alinxalinx/AXU2CGA_AXU2CGB/linux/.images_for_documents/60.png

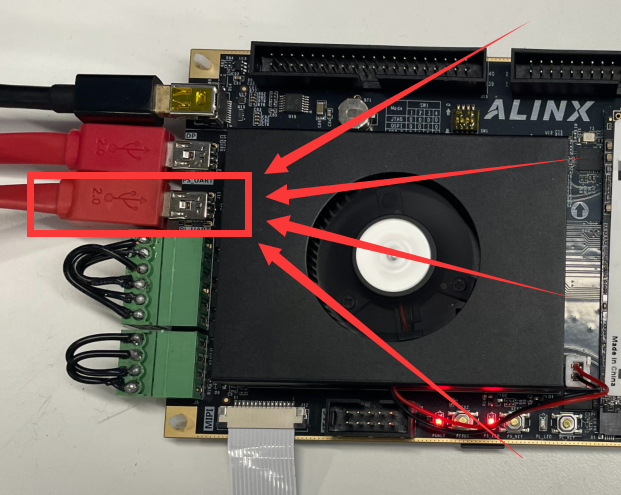
linux/.images_for_documents/60.png
