alinxalinx/AXU2CGA_AXU2CGB/linux/.images_for_documents/62.png

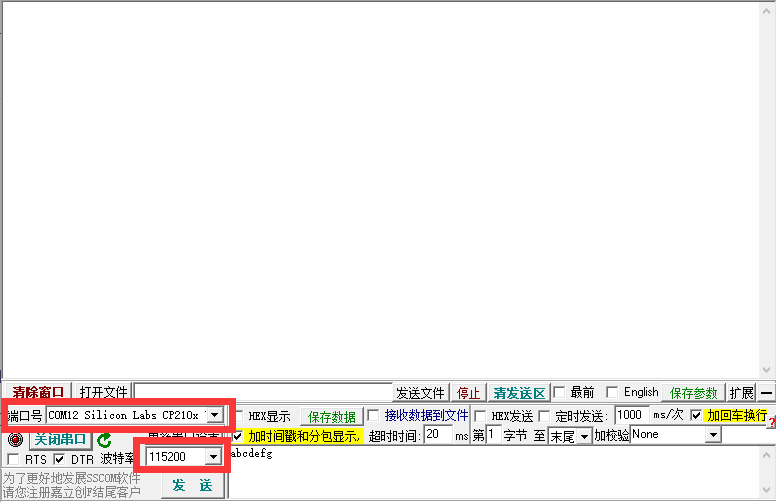
linux/.images_for_documents/62.png
